HeMatthias/E-Schaakbord/Bundel/Code_main_1_c.pdf

main.c

1 /* USER CODE BEGIN Header */
4 | * @file | : main.c
19 /* USER CODE END Header */
20 /* Includes ------------------------------------------------------------------*/ 21 #include "main.h"
22
23 /* Private includes ----------------------------------------------------------*/ 24 /* USER CODE BEGIN Includes */
25 #include "APA102C.h"
26 #include "MAX6955.h"
27
28 /* USER CODE END Includes */
29
30 /* Private typedef -----------------------------------------------------------*/ 31 /* USER CODE BEGIN PTD */
32
33 /* USER CODE END PTD */
34
35 /* Private define ------------------------------------------------------------*/ 36 /* USER CODE BEGIN PD */
37
38 /* USER CODE END PD */
39
40 /* Private macro -------------------------------------------------------------*/ 41 /* USER CODE BEGIN PM */
42
43 /* USER CODE END PM */
44
45 /* Private variables ---------------------------------------------------------*/ 46 I2C_HandleTypeDef hi2c2;
47
48 /* USER CODE BEGIN PV */
49 uint8_t buf[15];
50 /* USER CODE END PV */
51
52 /* Private function prototypes -----------------------------------------------*/ 53 void SystemClock_Config(void);
54 static void MX_GPIO_Init(void);
55 static void MX_I2C2_Init(void);
56 /* USER CODE BEGIN PFP */
57
58 /* USER CODE END PFP */
59
60 /* Private user code ---------------------------------------------------------*/ 61 /* USER CODE BEGIN 0 */

### 62 void SysTickDelayCount2(unsigned long ulCount){

63 CoreDebug->DEMCR |= CoreDebug_DEMCR_TRCENA_Msk;
64 ITM->LAR = 0xC5ACCE55;
65 DWT->CYCCNT = 0;
66 DWT->CTRL |= DWT_CTRL_CYCCNTENA_Msk;
67
68 while(DWT->CYCCNT < ulCount);
69 }
70 /*

### 71 void Meten(){

72 HAL_GPIO_WritePin(SPI1_CS_GPIO_Port,SPI1_CS_Pin,GPIO_PIN_RESET); 73 SysTickDelayCount2(t);

Page 1

main.c

74 HAL_GPIO_WritePin(SPI1_CS_GPIO_Port,SPI1_CS_Pin,GPIO_PIN_SET);

### 75 for (int8_t j = 0; j < 1; j++){ 76 for (int8_t i = 0; i < 8; i++){

77 SysTickDelayCount2((t/2));

### 78 buf[j][i] = (HAL_GPIO_ReadPin(SPI1_MISO_GPIO_Port,SPI1_MISO_Pin) ^ 1); //Inverteer

de lezing
79 SysTickDelayCount2((t/2));
80 HAL_GPIO_WritePin(SPI1_CLK_GPIO_Port,SPI1_CLK_Pin,GPIO_PIN_SET);
81 SysTickDelayCount2(t);
82 HAL_GPIO_WritePin(SPI1_CLK_GPIO_Port,SPI1_CLK_Pin,GPIO_PIN_RESET); 83 }
84 }
85 }
86 */
87 /* USER CODE END 0 */
88
89 /**
90 * @brief The application entry point. 91 * @retval int
92 */

### 93 int main(void)

94 {
95 /* USER CODE BEGIN 1 */ 96
97 /* USER CODE END 1 */
98
99 /* MCU Configuration--------------------------------------------------------*/ 100
101 /* Reset of all peripherals, Initializes the Flash interface and the Systick. */ 102 HAL_Init();
103
104 /* USER CODE BEGIN Init */
105
106 /* USER CODE END Init */
107
108 /* Configure the system clock */ 109 SystemClock_Config();
110
111 /* USER CODE BEGIN SysInit */ 112
113 /* USER CODE END SysInit */
114
115 /* Initialize all configured peripherals */ 116 MX_GPIO_Init();
117 MX_I2C2_Init();
118 /* USER CODE BEGIN 2 */
119
120 // 7-segment aansturen in test stand 121 SS_Start(1);
122
123 // APA102C's aansturen
124 LED_Start();
125 LED_Rood(10);
126 LED_Groen(10);
127 LED_Blauw(10);
128 LED_RGB(0, 10, 10);
129 LED_Start();

Page 2

main.c

130
131 /* USER CODE END 2 */
132
133 /* Infinite loop */
134 /* USER CODE BEGIN WHILE */ 135 while (1)
136 {
137 /* USER CODE END WHILE */ 138
139 /* USER CODE BEGIN 3 */ 140 }
141 /* USER CODE END 3 */
142 }
143
144 /**
145 * @brief System Clock Configuration 146 * @retval None
147 */
148 void SystemClock_Config(void)
149 {
150 RCC_OscInitTypeDef RCC_OscInitStruct = {0};
151 RCC_ClkInitTypeDef RCC_ClkInitStruct = {0};
152
153 /** Initializes the RCC Oscillators according to the specified parameters 154 * in the RCC_OscInitTypeDef structure.
155 */
156 RCC_OscInitStruct.OscillatorType = RCC_OSCILLATORTYPE_HSI;
157 RCC_OscInitStruct.HSIState = RCC_HSI_ON;
158 RCC_OscInitStruct.HSICalibrationValue = RCC_HSICALIBRATION_DEFAULT; 159 RCC_OscInitStruct.PLL.PLLState = RCC_PLL_ON;
160 RCC_OscInitStruct.PLL.PLLSource = RCC_PLLSOURCE_HSI_DIV2;
161 RCC_OscInitStruct.PLL.PLLMUL = RCC_PLL_MUL9;
162 if (HAL_RCC_OscConfig(&RCC_OscInitStruct) != HAL_OK) 163 {
164 Error_Handler();
165 }
166 /** Initializes the CPU, AHB and APB buses clocks
167 */
168 RCC_ClkInitStruct.ClockType = RCC_CLOCKTYPE_HCLK|RCC_CLOCKTYPE_SYSCLK 169 |RCC_CLOCKTYPE_PCLK1|RCC_CLOCKTYPE_PCLK2; 170 RCC_ClkInitStruct.SYSCLKSource = RCC_SYSCLKSOURCE_PLLCLK;
171 RCC_ClkInitStruct.AHBCLKDivider = RCC_SYSCLK_DIV1;
172 RCC_ClkInitStruct.APB1CLKDivider = RCC_HCLK_DIV1;
173 RCC_ClkInitStruct.APB2CLKDivider = RCC_HCLK_DIV1;
174
175 if (HAL_RCC_ClockConfig(&RCC_ClkInitStruct, FLASH_LATENCY_1) != HAL_OK) 176 {
177 Error_Handler();
178 }
179 }
180
181 /**
182 * @brief I2C2 Initialization Function 183 * @param None
184 * @retval None
185 */
186 static void MX_I2C2_Init(void)

Page 3

main.c

187 {
188
189 /* USER CODE BEGIN I2C2_Init 0 */ 190
191 /* USER CODE END I2C2_Init 0 */ 192
193 /* USER CODE BEGIN I2C2_Init 1 */ 194
195 /* USER CODE END I2C2_Init 1 */
196 hi2c2.Instance = I2C2;
197 hi2c2.Init.ClockSpeed = 100000;
198 hi2c2.Init.DutyCycle = I2C_DUTYCYCLE_2;
199 hi2c2.Init.OwnAddress1 = 0;
200 hi2c2.Init.AddressingMode = I2C_ADDRESSINGMODE_7BIT; 201 hi2c2.Init.DualAddressMode = I2C_DUALADDRESS_DISABLE; 202 hi2c2.Init.OwnAddress2 = 0;
203 hi2c2.Init.GeneralCallMode = I2C_GENERALCALL_DISABLE; 204 hi2c2.Init.NoStretchMode = I2C_NOSTRETCH_DISABLE; 205 if (HAL_I2C_Init(&hi2c2) != HAL_OK)
206 {
207 Error_Handler();
208 }
209 /* USER CODE BEGIN I2C2_Init 2 */ 210
211 /* USER CODE END I2C2_Init 2 */ 212
213 }
214
215 /**
216 * @brief GPIO Initialization Function 217 * @param None
218 * @retval None
219 */
220 static void MX_GPIO_Init(void)
221 {
222 GPIO_InitTypeDef GPIO_InitStruct = {0}; 223
224 /* GPIO Ports Clock Enable */
225 __HAL_RCC_GPIOC_CLK_ENABLE();
226 __HAL_RCC_GPIOA_CLK_ENABLE();
227 __HAL_RCC_GPIOB_CLK_ENABLE();
228
229 /*Configure GPIO pin Output Level */
230 HAL_GPIO_WritePin(SPI1_CS_GPIO_Port, SPI1_CS_Pin, GPIO_PIN_RESET); 231
232 /*Configure GPIO pin Output Level */
233 HAL_GPIO_WritePin(GPIOA, GPIO_PIN_2|SPI1_CLK_Pin, GPIO_PIN_RESET); 234
235 /*Configure GPIO pin Output Level */
236 HAL_GPIO_WritePin(GPIOB, SPI2_SCK_Pin|SPI2_MOSI_Pin, GPIO_PIN_RESET); 237
238 /*Configure GPIO pin : SPI1_CS_Pin */
239 GPIO_InitStruct.Pin = SPI1_CS_Pin;
240 GPIO_InitStruct.Mode = GPIO_MODE_OUTPUT_PP;
241 GPIO_InitStruct.Pull = GPIO_NOPULL;
242 GPIO_InitStruct.Speed = GPIO_SPEED_FREQ_HIGH;
243 HAL_GPIO_Init(SPI1_CS_GPIO_Port, &GPIO_InitStruct);

Page 4

main.c

244
245 /*Configure GPIO pins : PA2 SPI1_CLK_Pin */ 246 GPIO_InitStruct.Pin = GPIO_PIN_2|SPI1_CLK_Pin; 247 GPIO_InitStruct.Mode = GPIO_MODE_OUTPUT_PP; 248 GPIO_InitStruct.Pull = GPIO_NOPULL;
249 GPIO_InitStruct.Speed = GPIO_SPEED_FREQ_HIGH; 250 HAL_GPIO_Init(GPIOA, &GPIO_InitStruct);
251
252 /*Configure GPIO pin : SPI1_MISO_Pin */
253 GPIO_InitStruct.Pin = SPI1_MISO_Pin;
254 GPIO_InitStruct.Mode = GPIO_MODE_INPUT;
255 GPIO_InitStruct.Pull = GPIO_NOPULL;
256 HAL_GPIO_Init(SPI1_MISO_GPIO_Port, &GPIO_InitStruct); 257
258 /*Configure GPIO pins : SPI2_SCK_Pin SPI2_MOSI_Pin */ 259 GPIO_InitStruct.Pin = SPI2_SCK_Pin|SPI2_MOSI_Pin; 260 GPIO_InitStruct.Mode = GPIO_MODE_OUTPUT_PP;
261 GPIO_InitStruct.Pull = GPIO_NOPULL;
262 GPIO_InitStruct.Speed = GPIO_SPEED_FREQ_HIGH; 263 HAL_GPIO_Init(GPIOB, &GPIO_InitStruct);
264
265 }
266
267 /* USER CODE BEGIN 4 */ 268
269 /* USER CODE END 4 */
270
271 /**
272 * @brief This function is executed in case of error occurrence. 273 * @retval None
274 */
275 void Error_Handler(void)
276 {
277 /* USER CODE BEGIN Error_Handler_Debug */
278 /* User can add his own implementation to report the HAL error return state */ 279 __disable_irq();
280 while (1)
281 {
282 }
283 /* USER CODE END Error_Handler_Debug */ 284 }
285
286 #ifdef USE_FULL_ASSERT
287 /**
288 * @brief Reports the name of the source file and the source line number
289 * | where the assert_param error has occurred.
290 * @param file: pointer to the source file name
291 * @param line: assert_param error line source number
292 * @retval None
293 */
294 void assert_failed(uint8_t *file, uint32_t line)
295 {
296 /* USER CODE BEGIN 6 */
297 /* User can add his own implementation to report the file name and line number, 298 ex: printf("Wrong parameters value: file %s on line %d\r\n", file, line) */ 299 /* USER CODE END 6 */
300 }
| Page 5

main.c

301 #endif /* USE_FULL_ASSERT */
302
303 /************************ (C) COPYRIGHT STMicroelectronics *****END OF FILE****/ 304

Page 6
