HeMatthias/E-Schaakbord/Bundel/Berekening verbruik.pdf

Uin(V) Uled(V) Duty Cycle Iled(mA) Ndigit | Itot(mA) Ptot(mW)
3,3 | 2 | 0,9375 | 25 | 8 | 73,899 | 243,866
Uin(V) Iin(mA) Aantal | Itot(A) | Ptot(W)
5 | 73,5 | 64 | 4,704 | 23,52
Uin(V) Iin(mA) | Itot(mA) Ptot(mW)
3,3 | 20 | | 20 | 66
Uin(V) Iin(mA) Aantal | Itot(mA) Ptot(mW)
3,3 | 3 | 64 | 192 | 633,6
Uin(V) Uuit(V) Iq(mA) | Itot(mA) Ptot(mW)
5,2 | 3,2 | 10 | 20 | 40

Vermogen berekening*
MAX6955 (7 Segment Driver)

STM32F101RDTx (µC)

(*) De totale stromen onder 1mA wordt niet meegerekent. (EEPROM, Shift Register en Voltage Translator)

3V3 voor LDO

5V voor Schakelende voeding

APA102C (RGB Addressable LED's)

Imax(mA) | Pmax(W)

Imax(mA)
305,899

Pmax(mW)
983,466

NCP1117 (LDO)

5,010 | 24,503

AH3572 (Magnetic Sensor)
