HeMatthias/E-Schaakbord/Bundel/Code_main_2_c.pdf

main.c

1 /* USER CODE BEGIN Header */
4 | * @file | : main.c
19 /* USER CODE END Header */
20 /* Includes ------------------------------------------------------------------*/ 21 #include "main.h"
22
23 /* Private includes ----------------------------------------------------------*/ 24 /* USER CODE BEGIN Includes */
25
26 /* USER CODE END Includes */
27
28 /* Private typedef -----------------------------------------------------------*/ 29 /* USER CODE BEGIN PTD */
30
31 /* USER CODE END PTD */
32
33 /* Private define ------------------------------------------------------------*/ 34 /* USER CODE BEGIN PD */
35 #define t 1000
36 /* USER CODE END PD */
37
38 /* Private macro -------------------------------------------------------------*/ 39 /* USER CODE BEGIN PM */
40
41 /* USER CODE END PM */
42
43 /* Private variables ---------------------------------------------------------*/ 44
45 TIM_HandleTypeDef htim2;
46
47 UART_HandleTypeDef huart1; 48
49 /* USER CODE BEGIN PV */

### 50 uint8_t stand[8][8] = {

51 {02, 03, 04, 05, 06, 04, 03, 02}, 52 {01, 01, 01, 01, 01, 01, 01, 01}, 53 {00, 00, 00, 00, 00, 00, 00, 00}, 54 {00, 00, 00, 00, 00, 00, 00, 00}, 55 {00, 00, 00, 00, 00, 00, 00, 00}, 56 {00, 00, 00, 00, 00, 00, 00, 00}, 57 {10, 10, 10, 10, 10, 10, 10, 10}, 58 {20, 30, 40, 50, 60, 40, 30, 20} 59 };

### 60 uint8_t Bstand[8][8] = {

61 {02, 03, 04, 05, 06, 04, 03, 02}, 62 {01, 01, 01, 01, 01, 01, 01, 01}, 63 {00, 00, 00, 00, 00, 00, 00, 00}, 64 {00, 00, 00, 00, 00, 00, 00, 00}, 65 {00, 00, 00, 00, 00, 00, 00, 00}, 66 {00, 00, 00, 00, 00, 00, 00, 00}, 67 {10, 10, 10, 10, 10, 10, 10, 10}, 68 {20, 30, 40, 50, 60, 40, 30, 20} 69 };

### 70 uint8_t buf[8][8] = {

71 {00, 00, 00, 00, 00, 00, 00, 01}, 72 {01, 01, 01, 01, 01, 01, 01, 01}, 73 {00, 00, 00, 00, 00, 00, 00, 00},

Page 1

main.c

74 {00, 00, 00, 00, 00, 00, 00, 00}, 75 {00, 00, 00, 00, 00, 00, 00, 00}, 76 {00, 00, 00, 00, 00, 00, 00, 00}, 77 {01, 01, 01, 01, 01, 01, 01, 01}, 78 {01, 01, 01, 01, 01, 01, 01, 01} 79 };

### 80 uint8_t bufV[8][8] = {

81 {00, 00, 00, 00, 00, 00, 00, 01}, 82 {01, 01, 01, 01, 01, 01, 01, 01}, 83 {00, 00, 00, 00, 00, 00, 00, 00}, 84 {00, 00, 00, 00, 00, 00, 00, 00}, 85 {00, 00, 00, 00, 00, 00, 00, 00}, 86 {00, 00, 00, 00, 00, 00, 00, 00}, 87 {01, 01, 01, 01, 01, 01, 01, 01}, 88 {01, 01, 01, 01, 01, 01, 01, 01} 89 };
90 uint8_t coor[2];
91 uint8_t i = 0;
92 uint8_t j = 0;
93 uint8_t weg = 0;
94 /* USER CODE END PV */
95
96 /* Private function prototypes -----------------------------------------------*/ 97 void SystemClock_Config(void);
98 static void MX_GPIO_Init(void);
99 static void MX_TIM2_Init(void);
100 static void MX_USART1_UART_Init(void); 101 /* USER CODE BEGIN PFP */
102
103 /* USER CODE END PFP */
104
105 /* Private user code ---------------------------------------------------------*/ 106 /* USER CODE BEGIN 0 */
107 #include <errno.h>
108 #include <sys/stat.h>
109 #include <sys/times.h>
110 #include <sys/unistd.h>
111 int _write(int file, char *ptr, int len) { 112 HAL_StatusTypeDef xStatus;
113 switch (file) {
114 case STDOUT_FILENO: /*stdout*/
115 xStatus = HAL_UART_Transmit(&huart1, (uint8_t*)ptr, len, HAL_MAX_DELAY); 116 if (xStatus != HAL_OK) {
117 errno = EIO;
118 return -1;
119 }
120 break;
121 case STDERR_FILENO: /* stderr */
122 xStatus = HAL_UART_Transmit(&huart1, (uint8_t*)ptr, len, HAL_MAX_DELAY); 123 if (xStatus != HAL_OK) {
124 errno = EIO;
125 return -1;
126 }
127 break;
128 default:
129 errno = EBADF;
130 return -1;

Page 2

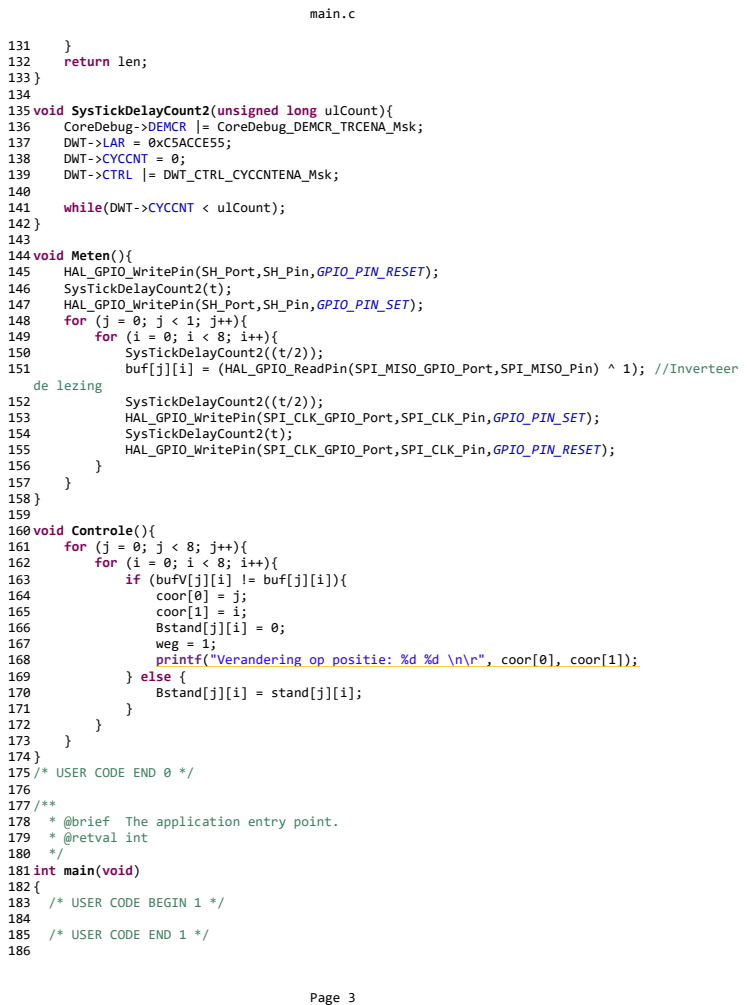
[picture p50: page 3]
main.c; 131 } 132 return len; 133 } 134 135 void SysTickDelayCount2(unsigned long ulCount){ 136 CoreDebug->DEMCR |= CoreDebug_DEMCR_TRCENA_Msk; 137 DWT->LAR = 0xC5ACCE55; 138 DWT->CYCCNT = 0; 139 DWT->CTRL |= DWT_CTRL_CYCCNTENA_Msk; 140 141 while(DWT->CYCCNT < ulCount); 142 } 143 144 void Meten(){ 145 HAL_GPIO_WritePin(SH_Port,SH_Pin,GPIO_PIN_RESET); 146 SysTickDelayCount2(t); 147 HAL_GPIO_WritePin(SH_Port,SH_Pin,GPIO_PIN_SET); 148 for (j = 0; j < 1; j++){ 149 for (i = 0; i < 8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

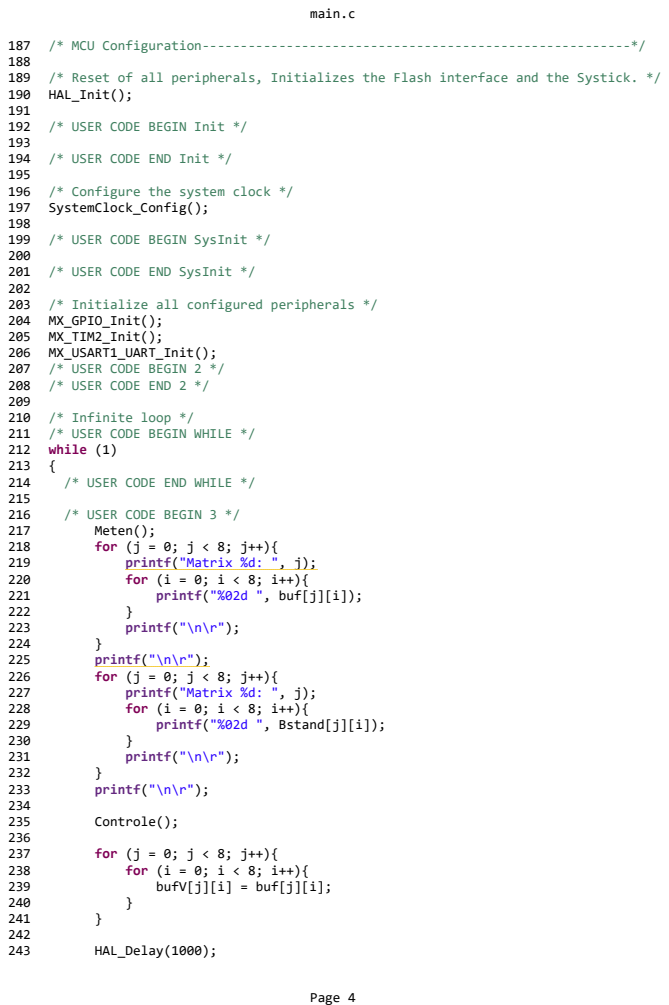
[picture p51: page 4]
main.c; 187 /* MCU Configuration--------------------------------------------------------*/ 188 189 /* Reset of all peripherals, Initializes the Flash interface and the Systick. */ 190 HAL_Init(); 191 192 /* USER CODE BEGIN Init */ 193 194 /* USER CODE END Init */ 195 196 /* Configure the system clock */ 197 SystemClock_Config(); 198 199 /* USER CODE BEGIN SysInit */ 200 201 /* USER CODE END SysInit */ 202 203 /* Initialize all configured peripherals */ 204 MX_GPIO_Init(); 205 MX_TIM2_Init()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

main.c

244
245 }
246 /* USER CODE END 3 */
247 }
248
249 /**
250 * @brief System Clock Configuration 251 * @retval None
252 */
253 void SystemClock_Config(void)
254 {
255 RCC_OscInitTypeDef RCC_OscInitStruct = {0};
256 RCC_ClkInitTypeDef RCC_ClkInitStruct = {0};
257 RCC_PeriphCLKInitTypeDef PeriphClkInitStruct = {0}; 258
259 /** Configure LSE Drive Capability
260 */
261 HAL_PWR_EnableBkUpAccess();
262 /** Configure the main internal regulator output voltage
263 */
264 __HAL_RCC_PWR_CLK_ENABLE();
265 __HAL_PWR_VOLTAGESCALING_CONFIG(PWR_REGULATOR_VOLTAGE_SCALE1);
266 /** Initializes the RCC Oscillators according to the specified parameters 267 * in the RCC_OscInitTypeDef structure.
268 */
269 RCC_OscInitStruct.OscillatorType = RCC_OSCILLATORTYPE_HSI;
270 RCC_OscInitStruct.HSIState = RCC_HSI_ON;
271 RCC_OscInitStruct.HSICalibrationValue = RCC_HSICALIBRATION_DEFAULT; 272 RCC_OscInitStruct.PLL.PLLState = RCC_PLL_ON;
273 RCC_OscInitStruct.PLL.PLLSource = RCC_PLLSOURCE_HSI;
274 RCC_OscInitStruct.PLL.PLLM = 8;
275 RCC_OscInitStruct.PLL.PLLN = 200;
276 RCC_OscInitStruct.PLL.PLLP = RCC_PLLP_DIV2;
277 RCC_OscInitStruct.PLL.PLLQ = 2;
278 if (HAL_RCC_OscConfig(&RCC_OscInitStruct) != HAL_OK) 279 {
280 Error_Handler();
281 }
282 /** Activate the Over-Drive mode
283 */
284 if (HAL_PWREx_EnableOverDrive() != HAL_OK) 285 {
286 Error_Handler();
287 }
288 /** Initializes the CPU, AHB and APB buses clocks
289 */
290 RCC_ClkInitStruct.ClockType = RCC_CLOCKTYPE_HCLK|RCC_CLOCKTYPE_SYSCLK 291 |RCC_CLOCKTYPE_PCLK1|RCC_CLOCKTYPE_PCLK2; 292 RCC_ClkInitStruct.SYSCLKSource = RCC_SYSCLKSOURCE_PLLCLK;
293 RCC_ClkInitStruct.AHBCLKDivider = RCC_SYSCLK_DIV1;
294 RCC_ClkInitStruct.APB1CLKDivider = RCC_HCLK_DIV4;
295 RCC_ClkInitStruct.APB2CLKDivider = RCC_HCLK_DIV2;
296
297 if (HAL_RCC_ClockConfig(&RCC_ClkInitStruct, FLASH_LATENCY_6) != HAL_OK) 298 {
299 Error_Handler();
300 }

Page 5

main.c

301 PeriphClkInitStruct.PeriphClockSelection = RCC_PERIPHCLK_USART1; 302 PeriphClkInitStruct.Usart1ClockSelection = RCC_USART1CLKSOURCE_PCLK2; 303 if (HAL_RCCEx_PeriphCLKConfig(&PeriphClkInitStruct) != HAL_OK)
304 {
305 Error_Handler();
306 }
307 }
308
309 /**
310 * @brief TIM2 Initialization Function 311 * @param None
312 * @retval None
313 */
314 static void MX_TIM2_Init(void)
315 {
316
317 /* USER CODE BEGIN TIM2_Init 0 */ 318
319 /* USER CODE END TIM2_Init 0 */
320
321 TIM_ClockConfigTypeDef sClockSourceConfig = {0}; 322 TIM_MasterConfigTypeDef sMasterConfig = {0}; 323
324 /* USER CODE BEGIN TIM2_Init 1 */
325
326 /* USER CODE END TIM2_Init 1 */
327 htim2.Instance = TIM2;
328 htim2.Init.Prescaler = 0;
329 htim2.Init.CounterMode = TIM_COUNTERMODE_DOWN;
330 htim2.Init.Period = 650;
331 htim2.Init.ClockDivision = TIM_CLOCKDIVISION_DIV1;
332 htim2.Init.AutoReloadPreload = TIM_AUTORELOAD_PRELOAD_ENABLE; 333 if (HAL_TIM_Base_Init(&htim2) != HAL_OK)
334 {
335 Error_Handler();
336 }
337 sClockSourceConfig.ClockSource = TIM_CLOCKSOURCE_INTERNAL;
338 if (HAL_TIM_ConfigClockSource(&htim2, &sClockSourceConfig) != HAL_OK) 339 {
340 Error_Handler();
341 }
342 sMasterConfig.MasterOutputTrigger = TIM_TRGO_RESET;
343 sMasterConfig.MasterSlaveMode = TIM_MASTERSLAVEMODE_DISABLE;
344 if (HAL_TIMEx_MasterConfigSynchronization(&htim2, &sMasterConfig) != HAL_OK) 345 {
346 Error_Handler();
347 }
348 /* USER CODE BEGIN TIM2_Init 2 */ 349
350 /* USER CODE END TIM2_Init 2 */ 351
352 }
353
354 /**
355 * @brief USART1 Initialization Function 356 * @param None
357 * @retval None

Page 6

main.c

358 */
359 static void MX_USART1_UART_Init(void) 360 {
361
362 /* USER CODE BEGIN USART1_Init 0 */ 363
364 /* USER CODE END USART1_Init 0 */ 365
366 /* USER CODE BEGIN USART1_Init 1 */ 367
368 /* USER CODE END USART1_Init 1 */
369 huart1.Instance = USART1;
370 huart1.Init.BaudRate = 115200;
371 huart1.Init.WordLength = UART_WORDLENGTH_8B; 372 huart1.Init.StopBits = UART_STOPBITS_1; 373 huart1.Init.Parity = UART_PARITY_NONE;
374 huart1.Init.Mode = UART_MODE_TX_RX;
375 huart1.Init.HwFlowCtl = UART_HWCONTROL_NONE;
376 huart1.Init.OverSampling = UART_OVERSAMPLING_16;
377 huart1.Init.OneBitSampling = UART_ONE_BIT_SAMPLE_DISABLE; 378 huart1.AdvancedInit.AdvFeatureInit = UART_ADVFEATURE_NO_INIT; 379 if (HAL_UART_Init(&huart1) != HAL_OK)
380 {
381 Error_Handler();
382 }
383 /* USER CODE BEGIN USART1_Init 2 */ 384
385 /* USER CODE END USART1_Init 2 */ 386
387 }
388
389 /**
390 * @brief GPIO Initialization Function 391 * @param None
392 * @retval None
393 */
394 static void MX_GPIO_Init(void)
395 {
396 GPIO_InitTypeDef GPIO_InitStruct = {0}; 397
398 /* GPIO Ports Clock Enable */
399 __HAL_RCC_GPIOI_CLK_ENABLE();
400 __HAL_RCC_GPIOA_CLK_ENABLE(); 401 __HAL_RCC_GPIOC_CLK_ENABLE(); 402 __HAL_RCC_GPIOH_CLK_ENABLE();
403 __HAL_RCC_GPIOB_CLK_ENABLE();
404
405 /*Configure GPIO pin Output Level */
406 HAL_GPIO_WritePin(SPI_CLK_PIN_GPIO_Port, SPI_CLK_PIN_Pin, GPIO_PIN_SET); 407
408 /*Configure GPIO pin Output Level */
409 HAL_GPIO_WritePin(SH_GPIO_Port, SH_Pin, GPIO_PIN_RESET);
410
411 /*Configure GPIO pin : SPI_CLK_PIN_Pin */
412 GPIO_InitStruct.Pin = SPI_CLK_PIN_Pin;
413 GPIO_InitStruct.Mode = GPIO_MODE_OUTPUT_PP; 414 GPIO_InitStruct.Pull = GPIO_PULLUP;

Page 7

main.c

415 GPIO_InitStruct.Speed = GPIO_SPEED_FREQ_VERY_HIGH; 416 HAL_GPIO_Init(SPI_CLK_PIN_GPIO_Port, &GPIO_InitStruct); 417
418 /*Configure GPIO pin : SPI_MISO_PIN_Pin */
419 GPIO_InitStruct.Pin = SPI_MISO_PIN_Pin;
420 GPIO_InitStruct.Mode = GPIO_MODE_INPUT;
421 GPIO_InitStruct.Pull = GPIO_NOPULL;
422 HAL_GPIO_Init(SPI_MISO_PIN_GPIO_Port, &GPIO_InitStruct); 423
424 /*Configure GPIO pin : SH_Pin */
425 GPIO_InitStruct.Pin = SH_Pin;
426 GPIO_InitStruct.Mode = GPIO_MODE_OUTPUT_PP;
427 GPIO_InitStruct.Pull = GPIO_PULLUP;
428 GPIO_InitStruct.Speed = GPIO_SPEED_FREQ_VERY_HIGH; 429 HAL_GPIO_Init(SH_GPIO_Port, &GPIO_InitStruct); 430
431 }
432
433 /* USER CODE BEGIN 4 */ 434
435 /* USER CODE END 4 */
436
437 /**
438 * @brief This function is executed in case of error occurrence. 439 * @retval None
440 */
441 void Error_Handler(void)
442 {
443 /* USER CODE BEGIN Error_Handler_Debug */
444 /* User can add his own implementation to report the HAL error return state */ 445 __disable_irq();
446 while (1)
447 {
448 }
449 /* USER CODE END Error_Handler_Debug */ 450 }
451
452 #ifdef USE_FULL_ASSERT
453 /**
454 * @brief Reports the name of the source file and the source line number
455 * | where the assert_param error has occurred.
456 * @param file: pointer to the source file name
457 * @param line: assert_param error line source number
458 * @retval None
459 */
460 void assert_failed(uint8_t *file, uint32_t line)
461 {
462 /* USER CODE BEGIN 6 */
463 /* User can add his own implementation to report the file name and line number, 464 ex: printf("Wrong parameters value: file %s on line %d\r\n", file, line) */ 465 /* USER CODE END 6 */
466 }
467 #endif /* USE_FULL_ASSERT */
468
469 /************************ (C) COPYRIGHT STMicroelectronics *****END OF FILE****/ 470

Page 8
