HeMatthias/E-Schaakbord/3D Simulatie/tex/1001-00.jpg

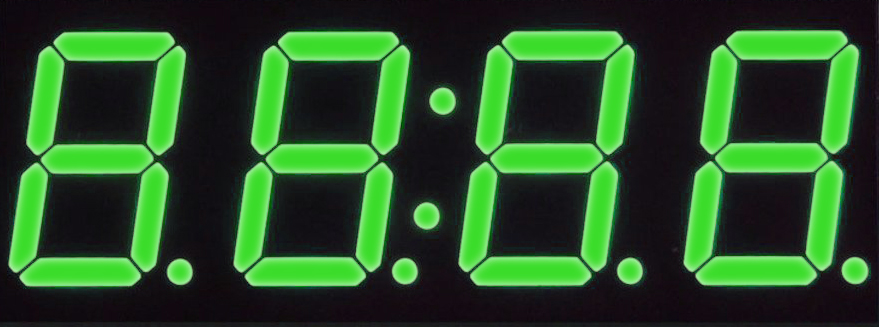
3D Simulatie/tex/1001-00.jpg
