HeMatthias/E-Schaakbord/Bundel/7-segment display.jpg

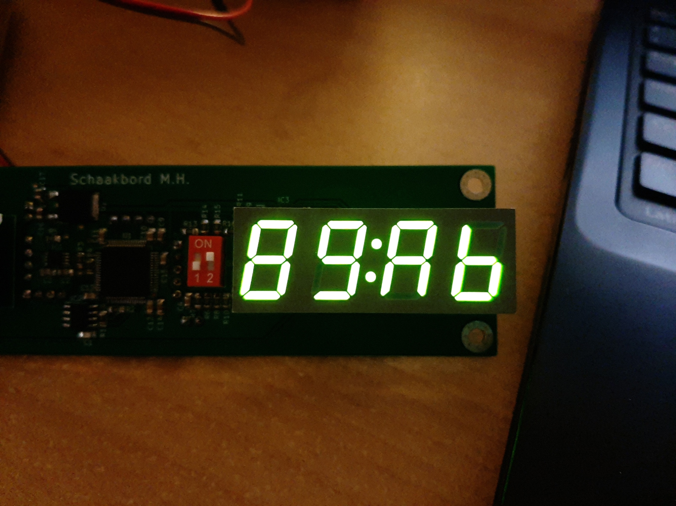
Bundel/7-segment display.jpg
