HeMatthias/E-Schaakbord/Bundel/plug.jpg

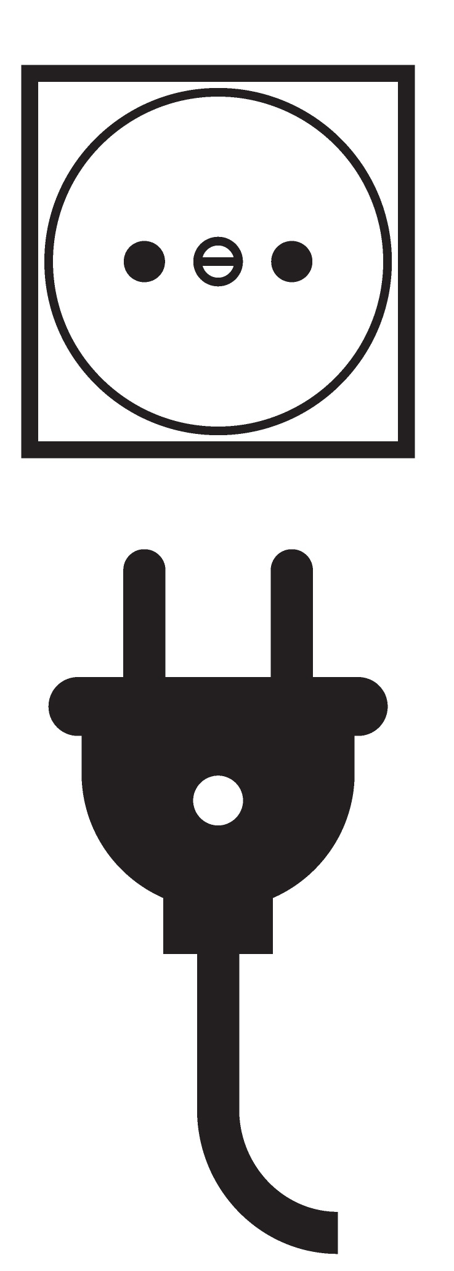
Bundel/plug.jpg
