HeMatthias/E-Schaakbord/Bundel/PSU.jpg

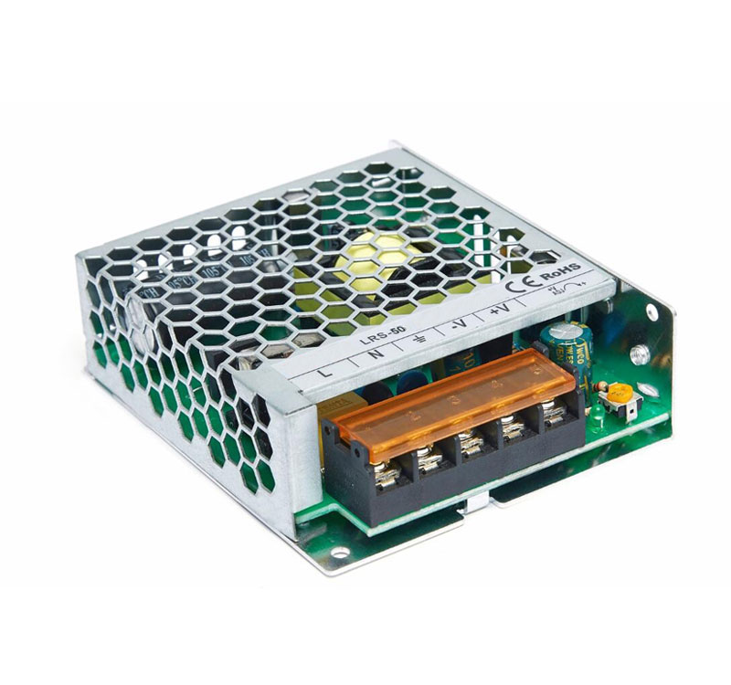
Bundel/PSU.jpg
