HeMatthias/E-Schaakbord/Bundel/pulsen-2.png

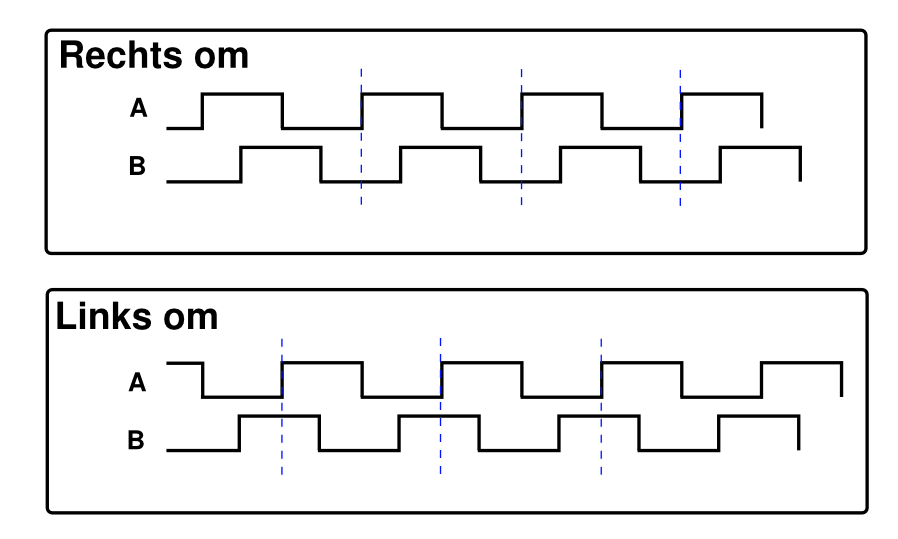
Bundel/pulsen-2.png
