HeMatthias/E-Schaakbord/VB Schaakbord4.jpg

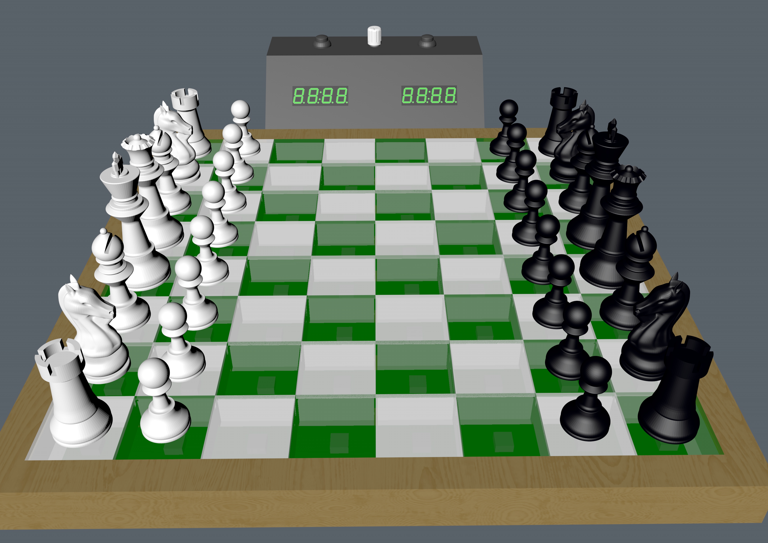
VB Schaakbord4.jpg
