HeMatthias/E-Schaakbord/Bundel/VT.pdf

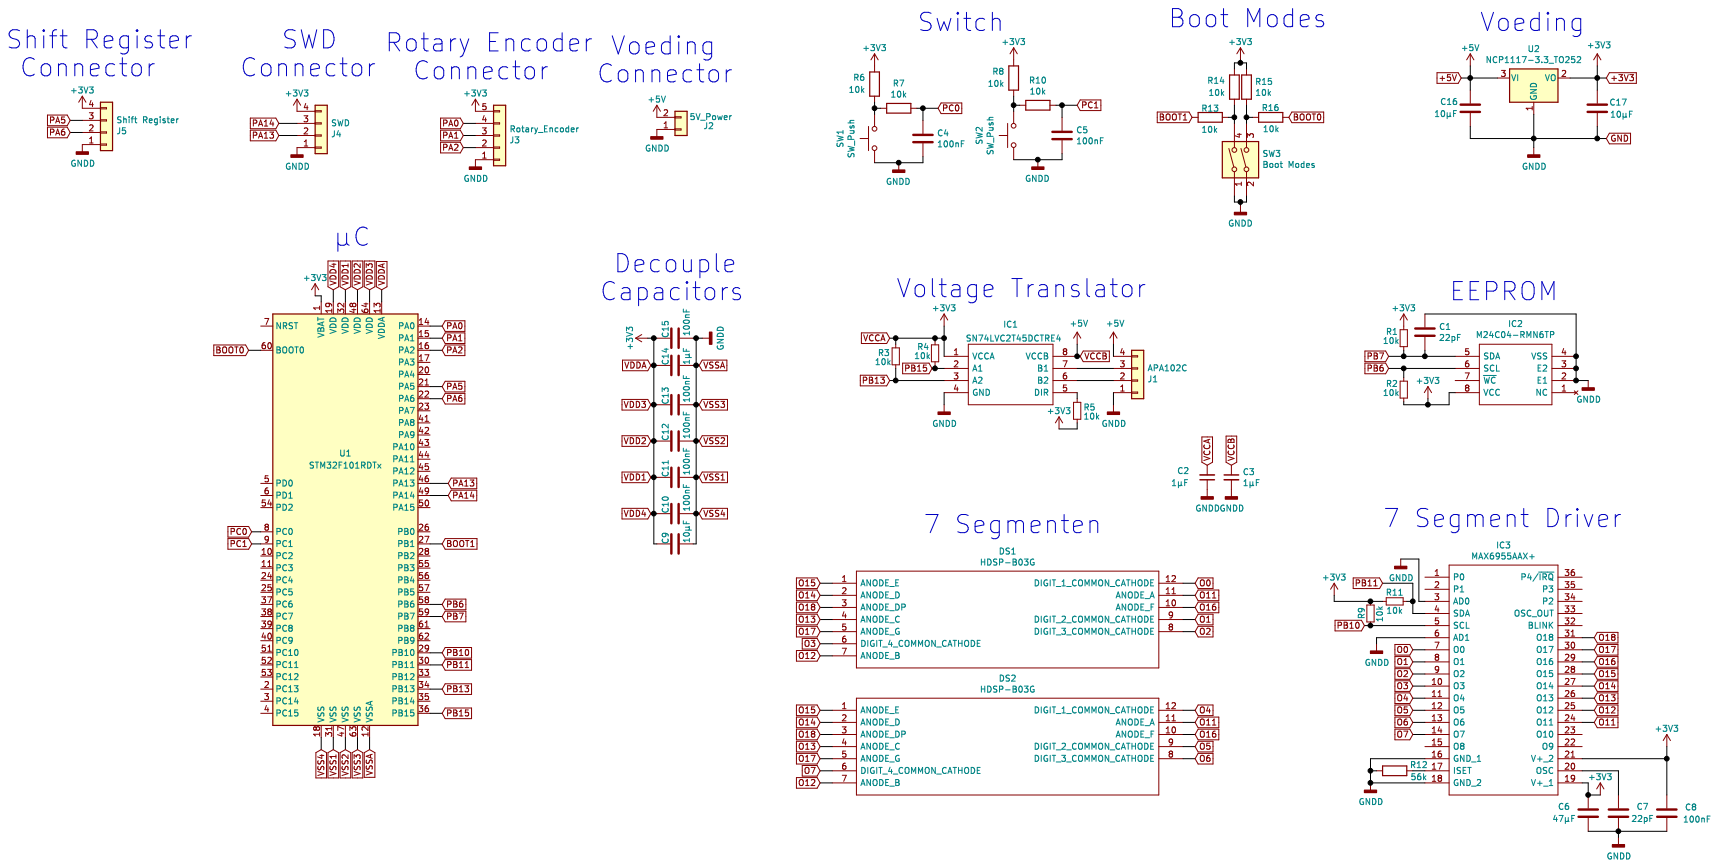
[picture p80: page 1]
