HeMatthias/E-Schaakbord/Bundel/schemas appart/rotary encoder/RE.pdf

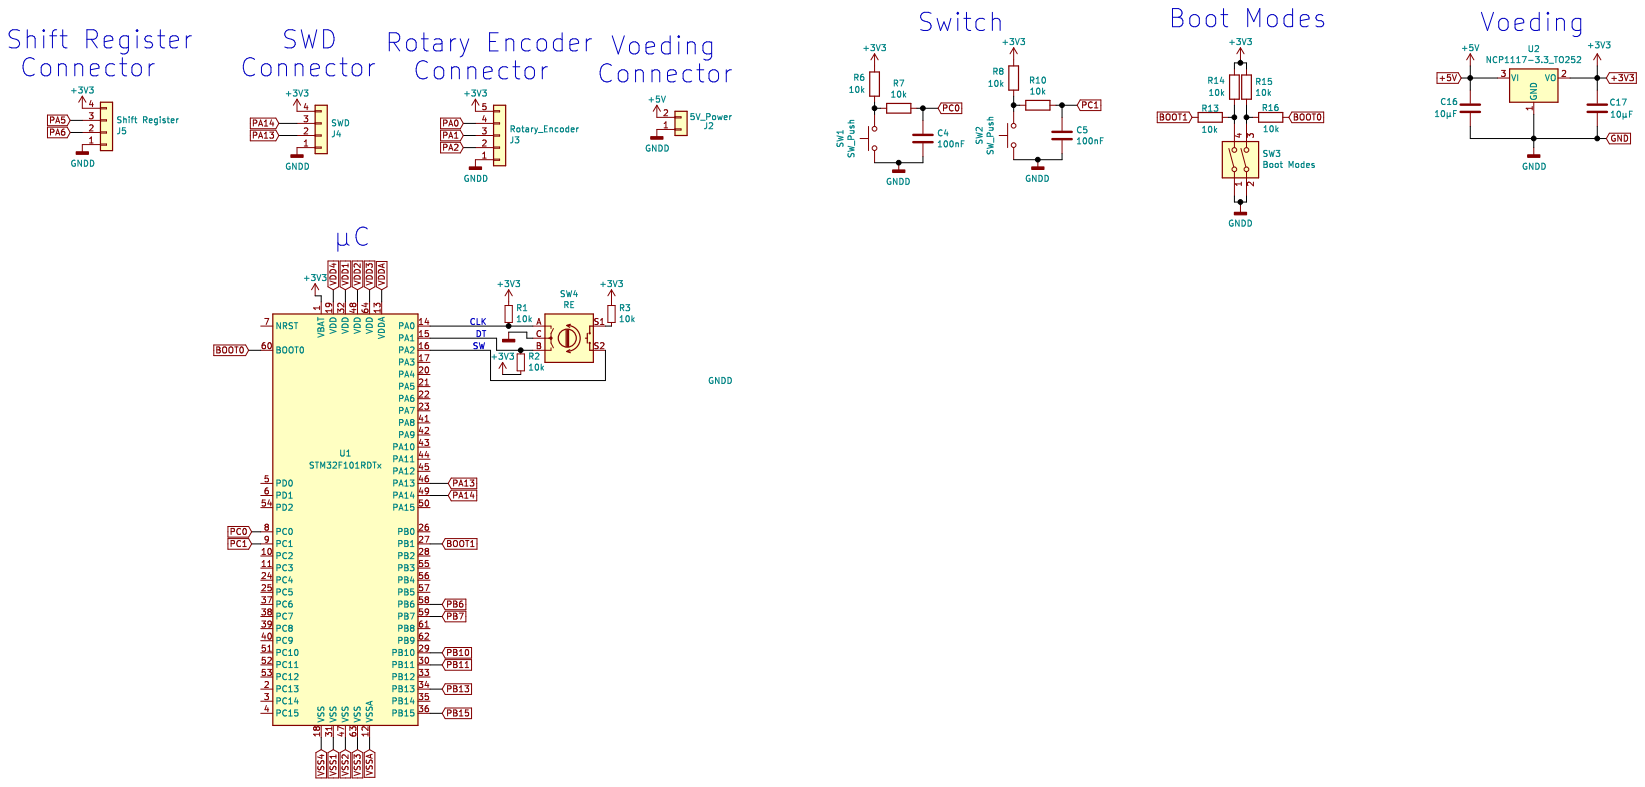
[picture p81: page 1]
