HeMatthias/E-Schaakbord/Bundel/schemas appart/Voltage Translator/VT.pdf

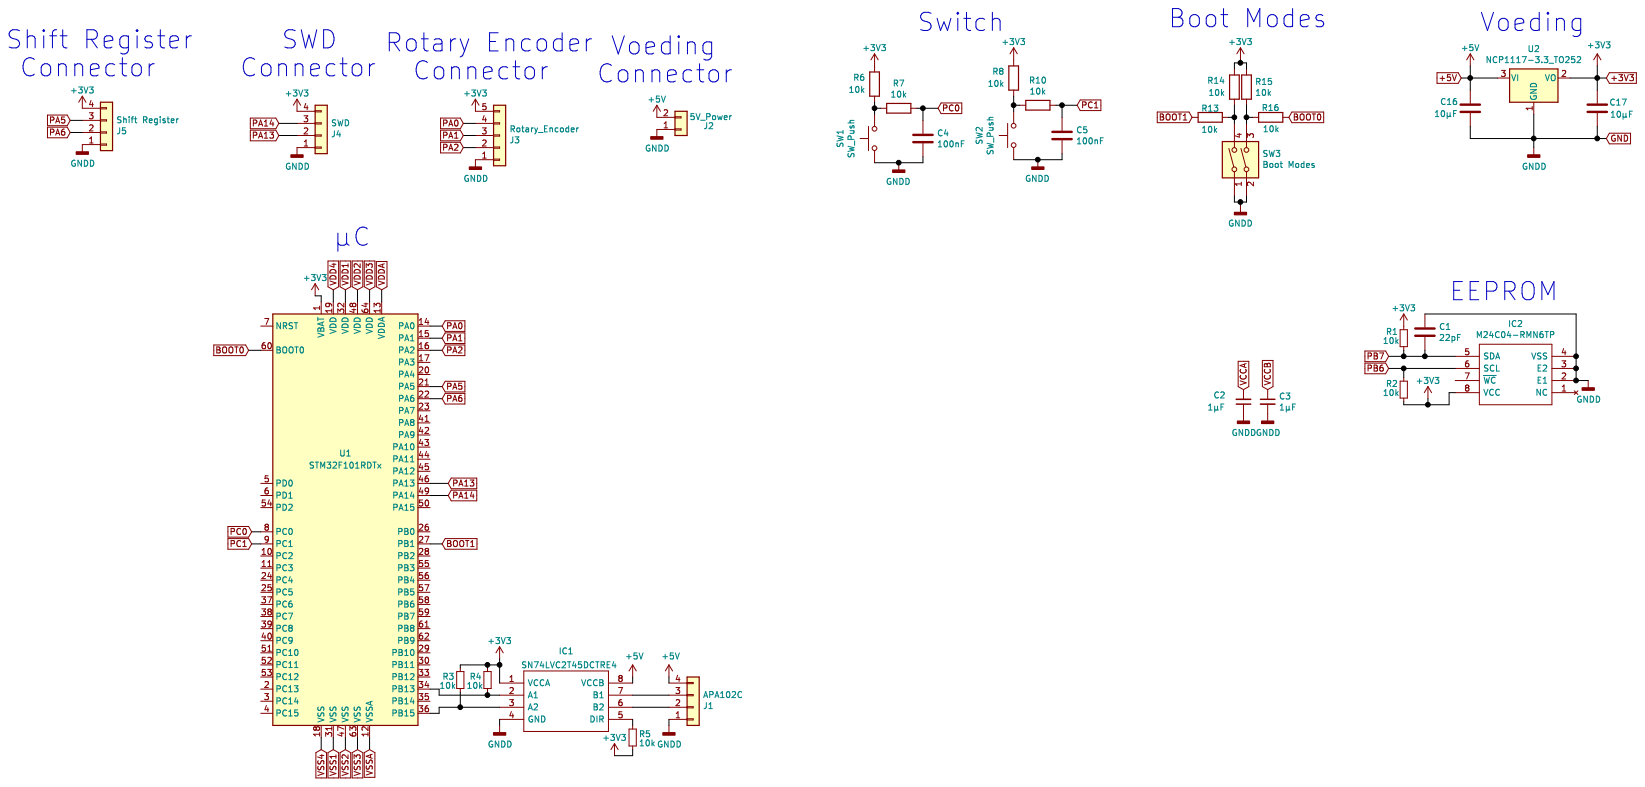
[picture p82: page 1]
