HeMatthias/E-Schaakbord/Code/Core/Inc/MAX6955.h

/*
 * MAX6955.h
 *
 *  Created on: 21 May 2021
 *      Author: Matthias
 */

#ifndef INC_MAX6955_H_
#define INC_MAX6955_H_

void SS_Start(uint8_t Test);
void SS_Schrijf(uint8_t digit, uint8_t getal, uint8_t DP);

#endif /* INC_MAX6955_H_ */
